inamilab/Magic-Stick/drone-stick/ball_table.h

uint8_t isinTable5[] = {
0,   4,   8,  12,  15,  18,  19,  20,  20,  19,  17,  14,  10,   6,
2,  -2,  -6, -10, -14, -17, -19, -20, -20, -19, -18, -15, -12,  -8,
-4,  -0, 0,   4,   8,  12,  15,  18,  19,  20,  20,  19,  17,  14,  10,   6,
2,  -2,  -6, -10, -14, -17, -19, -20, -20, -19, -18, -15, -12,  -8,
-4,  -0, 0,   4,   8,  12,  15,  18,  19,  20,  20,  19,  17,  14,  10,   6,
2,  -2,  -6, -10, -14, -17, -19, -20, -20, -19, -18, -15, -12,  -8,
-4,  -0, 0,   4,   8,  12,  15,  18,  19,  20,  20,  19,  17,  14,  10,   6,
2,  -2,  -6, -10, -14, -17, -19, -20, -20, -19, -18, -15, -12,  -8,
-4,  -0, 0,   4,   8,  12,  15,  18,  19,  20,  20,  19,  17,  14,  10,   6,
2,  -2,  -6, -10, -14, -17, -19, -20, -20, -19, -18, -15, -12,  -8,
-4,  -0, 0,   4,   8,  12,  15,  18,  19,  20,  20,  19,  17,  14,  10,   6,
2,  -2,  -6, -10, -14, -17, -19, -20, -20, -19, -18, -15, -12,  -8,
-4,  -0, 0,   4,   8,  12,  15,  18,  19,  20,  20,  19,  17,  14,  10,   6,
2,  -2,  -6, -10, -14, -17, -19, -20, -20, -19, -18, -15, -12,  -8,
-4,  -0, 0,   4,   8,  12,  15,  18,  19,  20,  20,  19,  17,  14,  10,   6,
2,  -2,  -6, -10, -14, -17, -19, -20, -20, -19, -18, -15, -12,  -8,
-4,  -0, 0,   4,   8,  12,  15,  18,  19,  20,  20,  19,  17,  14,  10,   6,
2,  -2,  -6, -10, -14, -17, -19, -20, -20, -19, -18, -15, -12,  -8,
-4,  -0, 0,   4,   8,  12,  15,  18,  19,  20,  20,  19,  17,  14,  10,   6,
2,  -2,  -6, -10, -14, -17, -19, -20, -20, -19, -18, -15, -12,  -8,
-4,  -0
};

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
//243, 243, 240, 234, 226, 215, 201, 185, 167, 147, 125, 102,  78,  52,
//26,   0,0,  26,  52,  78, 102, 125, 147, 167, 185, 201, 215, 226, 234, 240,
//243, 243, 240, 234, 226, 215, 201, 185, 167, 147, 125, 102,  78,  52,
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
//}; 
